frankyhub/Toni-Player/3D/Lade-Spacer.scad

cube(size = [17,10,4], center = true);
