frankyhub/Toni-Player/3D/RFID-Spacer.scad

/*
color("red") 
translate(v = [1, 0, 2]) {
cube(size = [46,40,1.5], center = true);
}
*/
cube(size = [48,50,3], center = true);

translate(v = [-34, 0, 0.5]) { 
cube(size = [24,50,4], center = true);
    }
