frankyhub/Toni-Player/3D/Spacer_20x5x5.scad

cube(size = [20,5,5], center = true);
