frankyhub/Toni-Player/Test/RFID_Auslesen_ESP_UNO/RFID_Auslesen_ESP_UNO.ino

/*************************************************************************************************
                                      PROGRAMMINFO
**************************************************************************************************
Funktion: RFID Auslesen
https://esp32io.com/tutorials/esp32-rfid-nfc
**************************************************************************************************
Version: 21.06.2022
**************************************************************************************************
Board: ESP32vn IoT Uno
**************************************************************************************************
Libraries:
https://github.com/espressif/arduino-esp32/tree/master/libraries
C:\Users\User\Documents\Arduino
D:\gittemp\Arduino II\A156_Wetterdaten_V3
**************************************************************************************************
C++ Arduino IDE V1.8.19

R2-D2
2QK384JVPX
**************************************************************************************************
Einstellungen:
https://dl.espressif.com/dl/package_esp32_index.json
http://dan.drown.org/stm32duino/package_STM32duino_index.json
http://arduino.esp8266.com/stable/package_esp8266com_index.json
**************************************************************************************************/

#include <SPI.h>
#include <MFRC522.h>

#define RST_PIN   4//27 // 22
#define SS_PIN    5 //  SDA 2 17 

/*ESP32 UNO
 * MISO 19
 * MOSI 23
 * SCK 18
 * RST 4
 * SDA 2
 */


MFRC522 rfid(SS_PIN, RST_PIN);

void setup() {
  Serial.begin(115200);
  SPI.begin(); // init SPI bus

  rfid.PCD_Init(); // init MFRC522

  Serial.println("Tap an RFID/NFC tag on the RFID-RC522 reader");
}

void loop() {
  if (rfid.PICC_IsNewCardPresent()) { // new tag is available
    if (rfid.PICC_ReadCardSerial()) { // NUID has been readed
      MFRC522::PICC_Type piccType = rfid.PICC_GetType(rfid.uid.sak);
      Serial.print("RFID/NFC Tag Type: ");
      Serial.println(rfid.PICC_GetTypeName(piccType));

      // print UID in Serial Monitor in the hex format
      Serial.print("UID:");
      for (int i = 0; i < rfid.uid.size; i++) {
        Serial.print(rfid.uid.uidByte[i] < 0x10 ? " 0" : " ");
        Serial.print(rfid.uid.uidByte[i], HEX);
      }
      Serial.println();

      rfid.PICC_HaltA(); // halt PICC
      rfid.PCD_StopCrypto1(); // stop encryption on PCD
    }
  }
}
